RobJansen62/Analog-Digital-Clock/pictures/P1000631.JPG

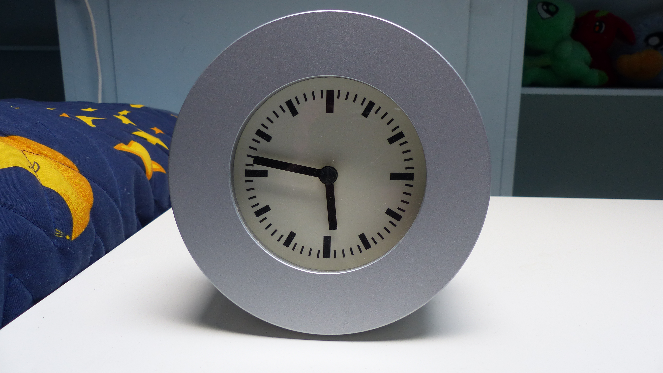
pictures/P1000631.JPG
