RobJansen62/Analog-Digital-Clock/pictures/P1000633.JPG

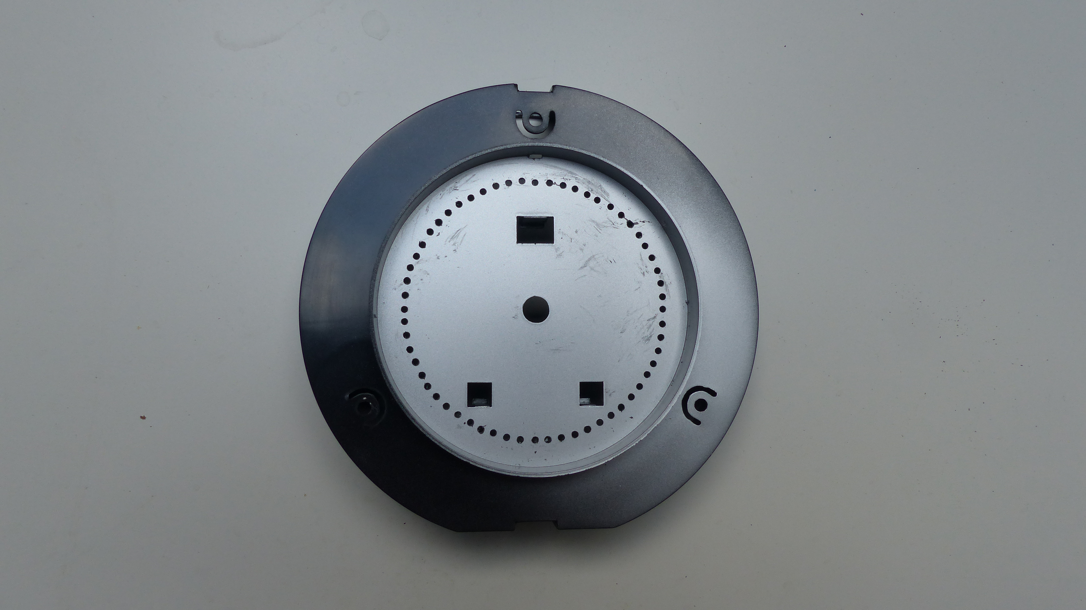
pictures/P1000633.JPG
