RobJansen62/Analog-Digital-Clock/pictures/P1000641.JPG

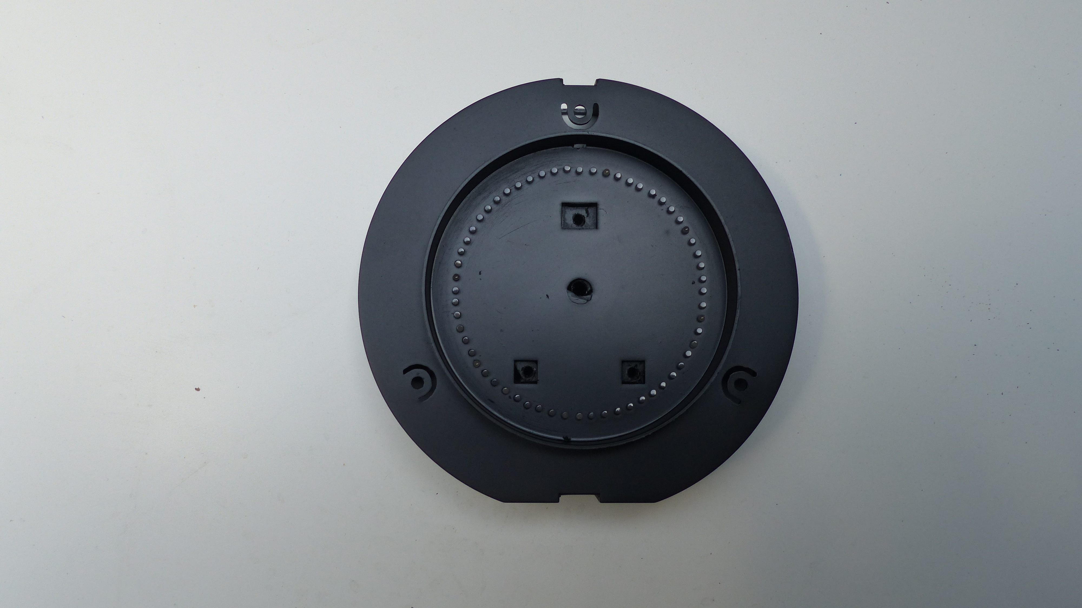
pictures/P1000641.JPG
