RobJansen62/Analog-Digital-Clock/pictures/P1000644.JPG

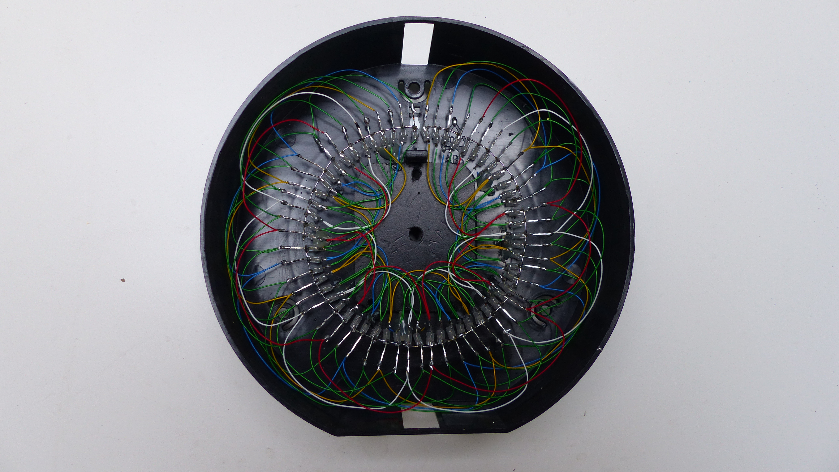
pictures/P1000644.JPG
