RobJansen62/Analog-Digital-Clock/pictures/P1000670.JPG

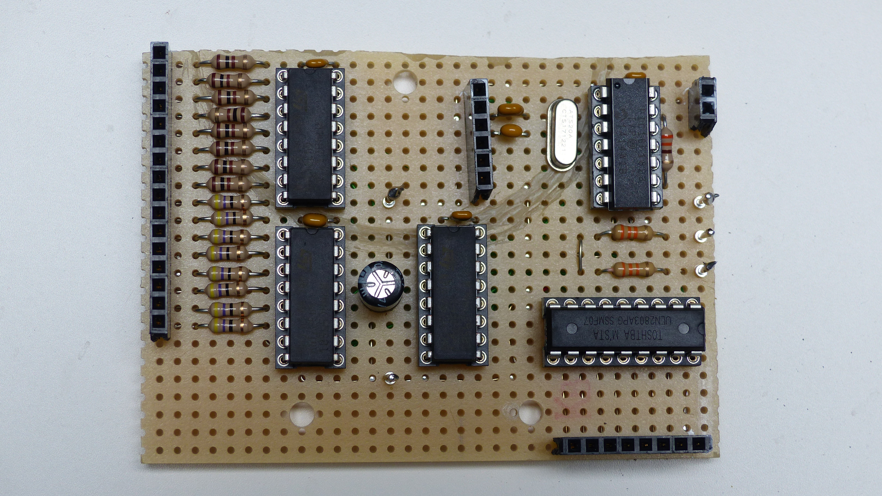
pictures/P1000670.JPG
