RobJansen62/Analog-Digital-Clock/pictures/P1000675.JPG

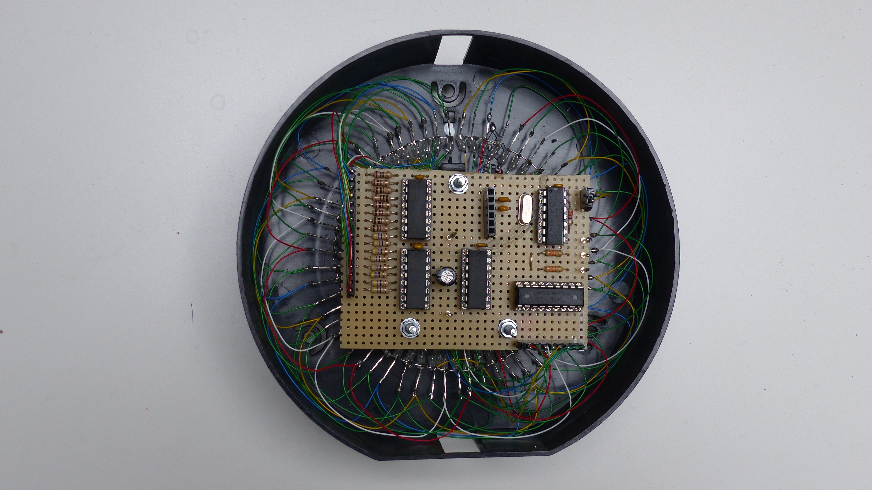
pictures/P1000675.JPG
