RobJansen62/Analog-Digital-Clock/hardware/Analog_Digital_Clock.kicad_sch

## KiCad design hardware/Analog_Digital_Clock.kicad_sch (2025-06-09)

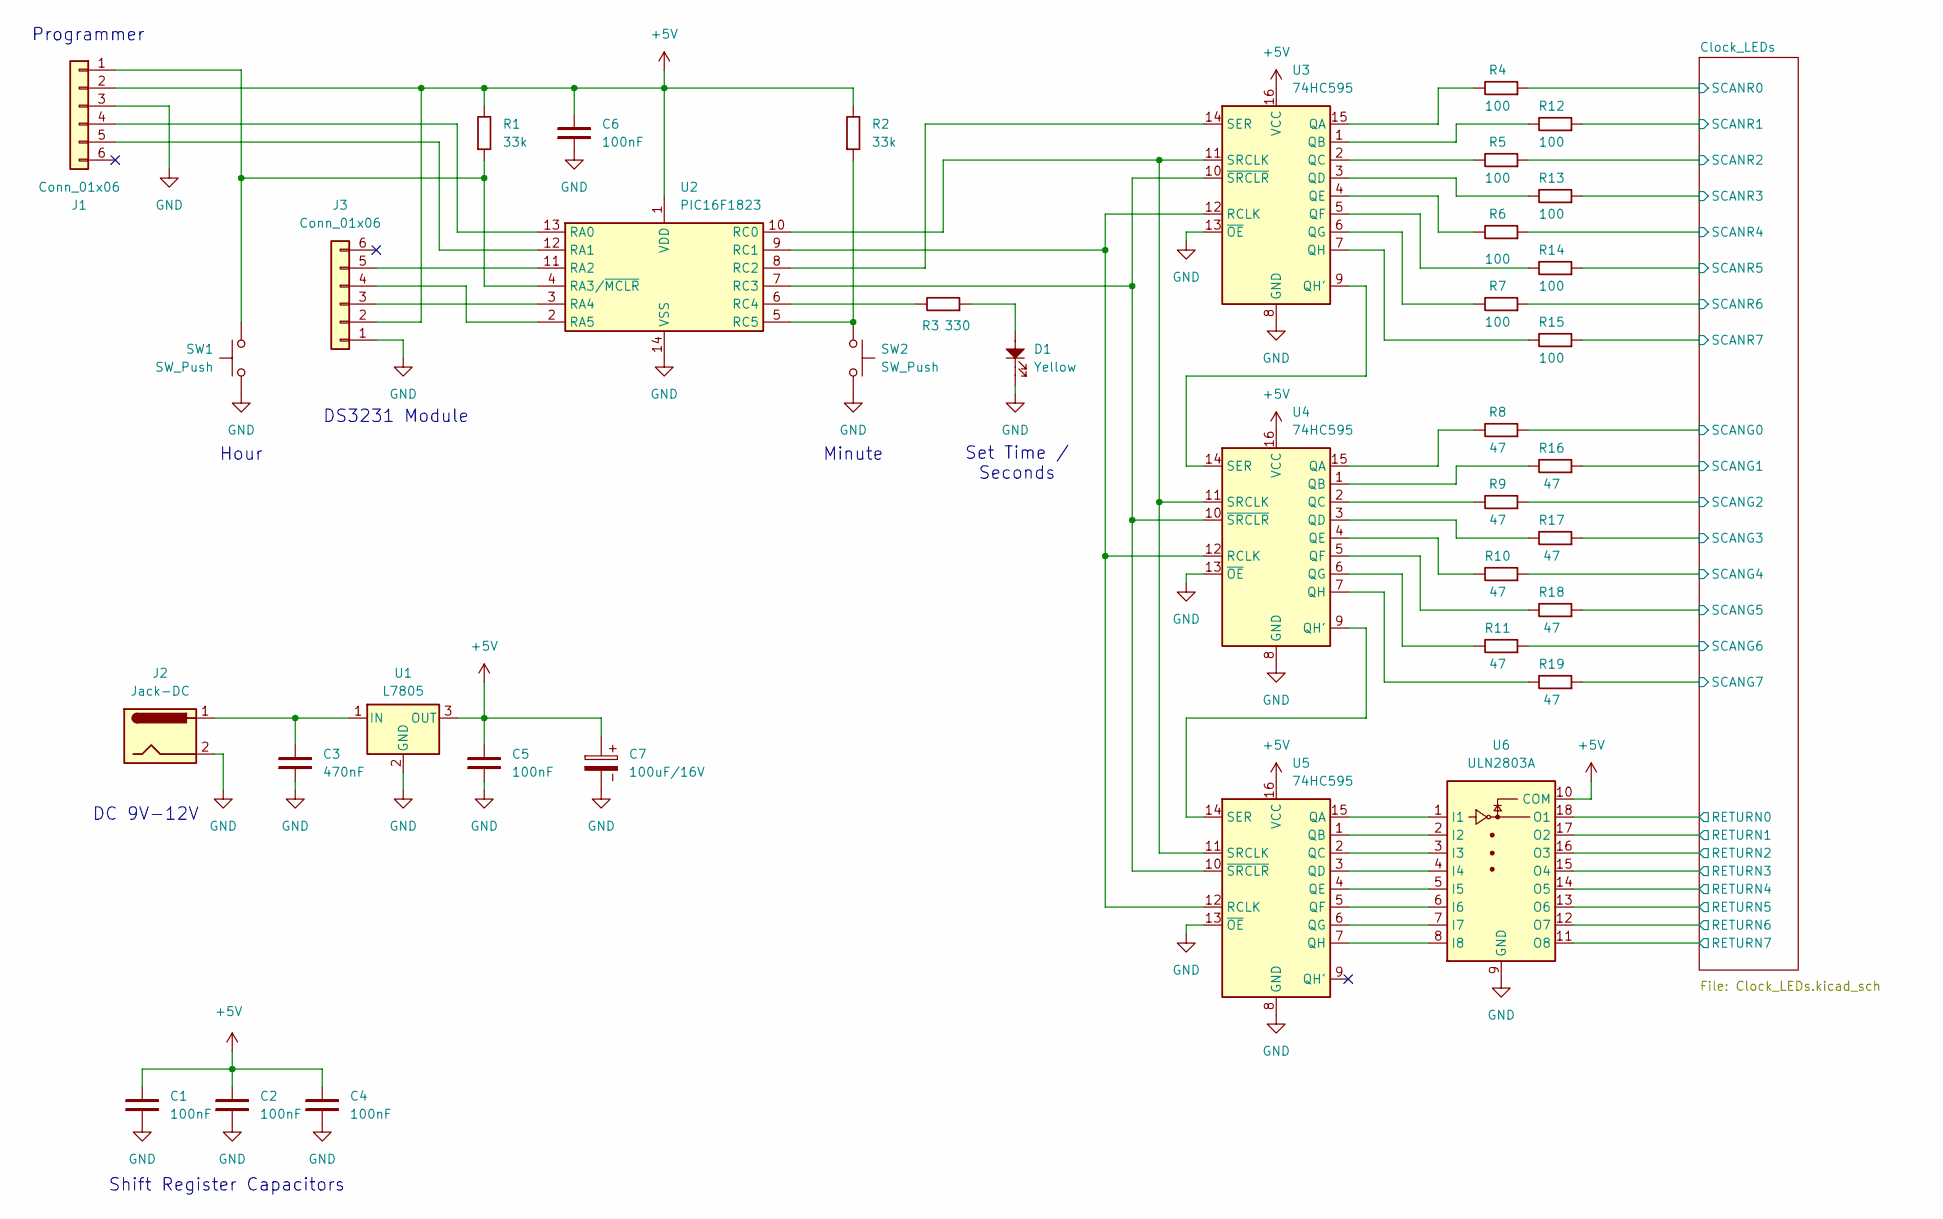
[picture p14: schematic Analog_Digital_Clock.kicad_sch]

Parts:
C1, C2, C4, C5, C6: 100nF; C_Disc_D5.0mm_W2.5mm_P2.50mm
C3: 470nF; C_Disc_D5.0mm_W2.5mm_P2.50mm
C7: 100uF/16V; CP_Radial_D5.0mm_P2.50mm
D1: Yellow; LED_D5.0mm
J1, J3: Conn_01x06
J2: Jack-DC
R1, R2: 33k; R_Axial_DIN0207_L6.3mm_D2.5mm_P10.16mm_Horizontal
R3: 330; R_Axial_DIN0207_L6.3mm_D2.5mm_P10.16mm_Horizontal
R4, R5, R6, R7, R12, R13, R14, R15: 100; R_Axial_DIN0207_L6.3mm_D2.5mm_P10.16mm_Horizontal
R8, R9, R10, R11, R16, R17, R18, R19: 47; R_Axial_DIN0207_L6.3mm_D2.5mm_P10.16mm_Horizontal
SW1, SW2: SW_Push
U1: L7805
U2: PIC16F1823; SOIC-14_3.9x8.7mm_P1.27mm
U3, U4, U5: 74HC595
U6: ULN2803A

Connections:
+5V: C1.2, C2.2, C4.2, C5.2, C6.2, C7.1, J1.2, J3.2, R1.2, R2.2, U1.3 (OUT), U2.1 (VDD), U3.16 (VCC), U4.16 (VCC), U5.16 (VCC), U6.10 (COM)
GND: C1.1, C2.1, C3.1, C4.1, C5.1, C6.1, C7.2, D1.1, J1.3, J2.2, J3.1, SW1.1, SW2.1, U1.2 (GND), U2.14 (VSS), U3.8 (GND), U3.13 (~OE), U4.8 (GND), U4.13 (~OE), U5.8 (GND), U5.13 (~OE), U6.9 (GND)
unnamed: C3.2, J2.1, U1.1 (IN)
unnamed: D1.2, R3.1
unnamed: J1.1, R1.1, SW1.2, U2.4 (RA3/~MCLR)
unnamed: J1.4, U2.13 (RA0)
unnamed: J1.5, U2.12 (RA1)
unnamed: J3.3, U2.3 (RA4)
unnamed: J3.4, U2.2 (RA5)
unnamed: J3.5, U2.11 (RA2)
unnamed: R2.1, SW2.2, U2.5 (RC5)
unnamed: R3.2, U2.6 (RC4)
unnamed: R4.2, U3.15 (QA)
unnamed: R5.2, U3.2 (QC)
unnamed: R6.2, U3.4 (QE)
unnamed: R7.2, U3.6 (QG)
unnamed: R8.2, U4.15 (QA)
unnamed: R9.2, U4.2 (QC)
unnamed: R10.2, U4.4 (QE)
unnamed: R11.2, U4.6 (QG)
unnamed: R12.2, U3.1 (QB)
unnamed: R13.2, U3.3 (QD)
unnamed: R14.2, U3.5 (QF)
unnamed: R15.2, U3.7 (QH)
unnamed: R16.2, U4.1 (QB)
unnamed: R17.2, U4.3 (QD)
unnamed: R18.2, U4.5 (QF)
unnamed: R19.2, U4.7 (QH)
unnamed: U2.7 (RC3), U3.10 (~SRCLR), U4.10 (~SRCLR), U5.10 (~SRCLR)
unnamed: U2.8 (RC2), U3.14 (SER)
unnamed: U2.9 (RC1), U3.12 (RCLK), U4.12 (RCLK), U5.12 (RCLK)
unnamed: U2.10 (RC0), U3.11 (SRCLK), U4.11 (SRCLK), U5.11 (SRCLK)
unnamed: U3.9 (QH'), U4.14 (SER)
unnamed: U4.9 (QH'), U5.14 (SER)
unnamed: U5.1 (QB), U6.2 (I2)
unnamed: U5.2 (QC), U6.3 (I3)
unnamed: U5.3 (QD), U6.4 (I4)
unnamed: U5.4 (QE), U6.5 (I5)
unnamed: U5.5 (QF), U6.6 (I6)
unnamed: U5.6 (QG), U6.7 (I7)
unnamed: U5.7 (QH), U6.8 (I8)
unnamed: U5.15 (QA), U6.1 (I1)
RETURN0: U6.18 (O1)
RETURN1: U6.17 (O2)
RETURN2: U6.16 (O3)
RETURN3: U6.15 (O4)
RETURN4: U6.14 (O5)
RETURN5: U6.13 (O6)
RETURN6: U6.12 (O7)
RETURN7: U6.11 (O8)
SCANG0: R8.1
SCANG1: R16.1
SCANG2: R9.1
SCANG3: R17.1
SCANG4: R10.1
SCANG5: R18.1
SCANG6: R11.1
SCANG7: R19.1
SCANR0: R4.1
SCANR1: R12.1
SCANR2: R5.1
SCANR3: R13.1
SCANR4: R6.1
SCANR5: R14.1
SCANR6: R7.1
SCANR7: R15.1

Notes on the sheet:
Hour
Set Time / Seconds
Shift Register Capacitors
Minute
DS3231 Module
DC 9V-12V
Programmer
