RobJansen62/Analog-Digital-Clock/hardware/Clock_LEDs.kicad_sch

## KiCad design hardware/Clock_LEDs.kicad_sch (2025-06-09)

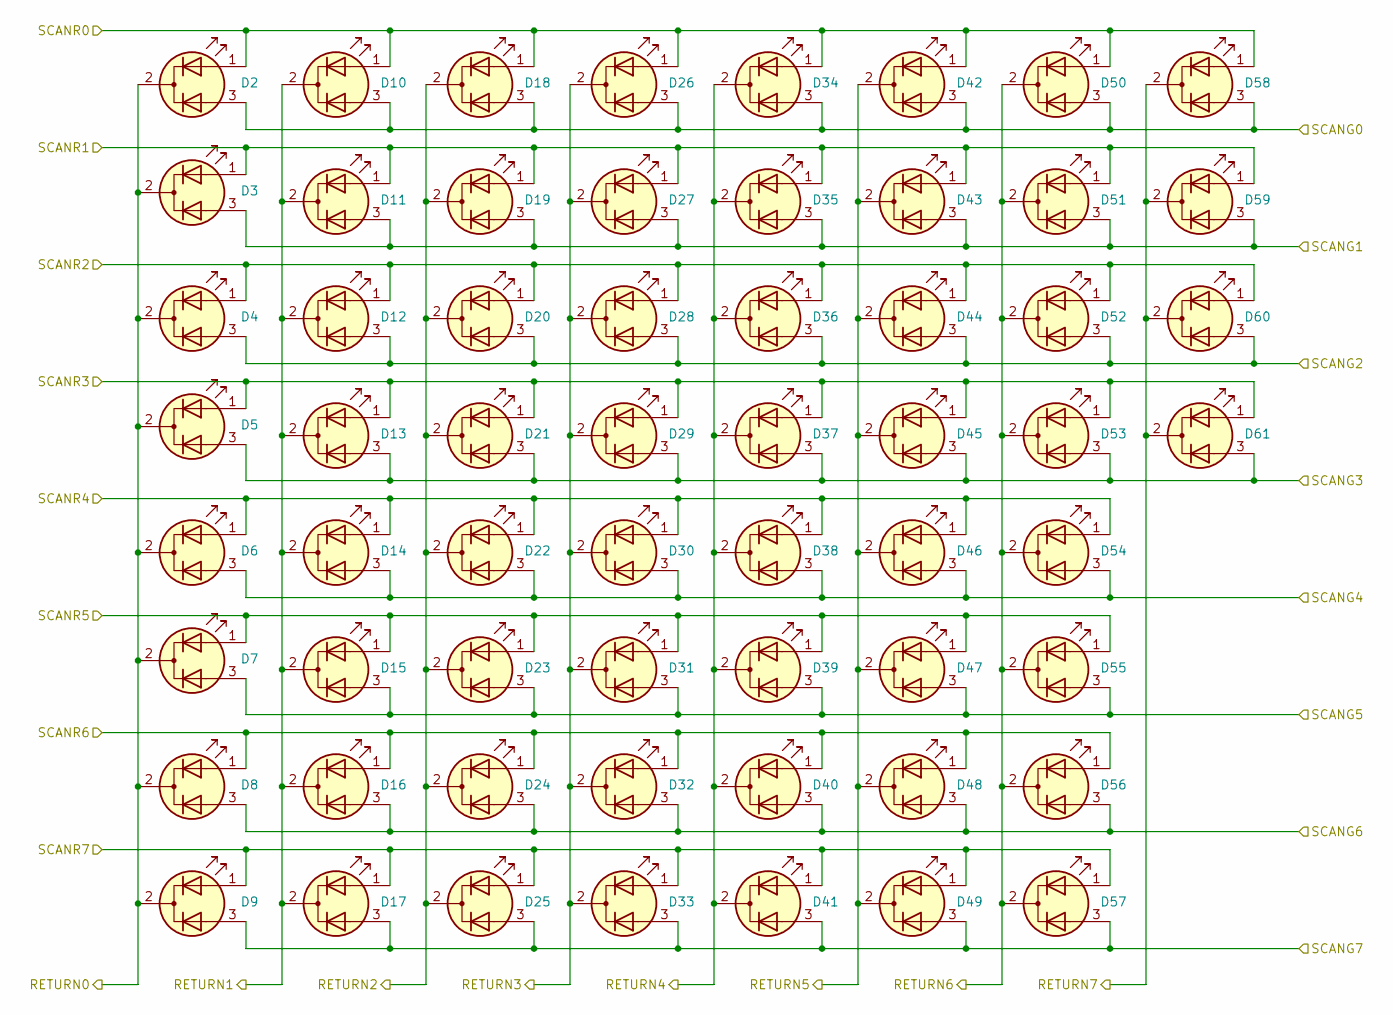
[picture p15: schematic Clock_LEDs.kicad_sch]

Parts:
D2, D3, D4, D5, D6, D7, D8, D9, D10, D11, D12, D13, D14, D15, D16, D17, D18, D19, D20, D21, D22, D23, D24, D25, D26, D27, D28, D29, D30, D31, D32, D33, D34, D35, D36, D37, D38, D39, D40, D41, D42, D43, D44, D45, D46, D47, D48, D49, D50, D51, D52, D53, D54, D55, D56, D57, D58, D59, D60, D61: LED_RG

Connections:
RETURN0: D2.2 (K), D3.2 (K), D4.2 (K), D5.2 (K), D6.2 (K), D7.2 (K), D8.2 (K), D9.2 (K)
RETURN1: D10.2 (K), D11.2 (K), D12.2 (K), D13.2 (K), D14.2 (K), D15.2 (K), D16.2 (K), D17.2 (K)
RETURN2: D18.2 (K), D19.2 (K), D20.2 (K), D21.2 (K), D22.2 (K), D23.2 (K), D24.2 (K), D25.2 (K)
RETURN3: D26.2 (K), D27.2 (K), D28.2 (K), D29.2 (K), D30.2 (K), D31.2 (K), D32.2 (K), D33.2 (K)
RETURN4: D34.2 (K), D35.2 (K), D36.2 (K), D37.2 (K), D38.2 (K), D39.2 (K), D40.2 (K), D41.2 (K)
RETURN5: D42.2 (K), D43.2 (K), D44.2 (K), D45.2 (K), D46.2 (K), D47.2 (K), D48.2 (K), D49.2 (K)
RETURN6: D50.2 (K), D51.2 (K), D52.2 (K), D53.2 (K), D54.2 (K), D55.2 (K), D56.2 (K), D57.2 (K)
RETURN7: D58.2 (K), D59.2 (K), D60.2 (K), D61.2 (K)
SCANG0: D2.3 (A2), D10.3 (A2), D18.3 (A2), D26.3 (A2), D34.3 (A2), D42.3 (A2), D50.3 (A2), D58.3 (A2)
SCANG1: D3.3 (A2), D11.3 (A2), D19.3 (A2), D27.3 (A2), D35.3 (A2), D43.3 (A2), D51.3 (A2), D59.3 (A2)
SCANG2: D4.3 (A2), D12.3 (A2), D20.3 (A2), D28.3 (A2), D36.3 (A2), D44.3 (A2), D52.3 (A2), D60.3 (A2)
SCANG3: D5.3 (A2), D13.3 (A2), D21.3 (A2), D29.3 (A2), D37.3 (A2), D45.3 (A2), D53.3 (A2), D61.3 (A2)
SCANG4: D6.3 (A2), D14.3 (A2), D22.3 (A2), D30.3 (A2), D38.3 (A2), D46.3 (A2), D54.3 (A2)
SCANG5: D7.3 (A2), D15.3 (A2), D23.3 (A2), D31.3 (A2), D39.3 (A2), D47.3 (A2), D55.3 (A2)
SCANG6: D8.3 (A2), D16.3 (A2), D24.3 (A2), D32.3 (A2), D40.3 (A2), D48.3 (A2), D56.3 (A2)
SCANG7: D9.3 (A2), D17.3 (A2), D25.3 (A2), D33.3 (A2), D41.3 (A2), D49.3 (A2), D57.3 (A2)
SCANR0: D2.1 (A1), D10.1 (A1), D18.1 (A1), D26.1 (A1), D34.1 (A1), D42.1 (A1), D50.1 (A1), D58.1 (A1)
SCANR1: D3.1 (A1), D11.1 (A1), D19.1 (A1), D27.1 (A1), D35.1 (A1), D43.1 (A1), D51.1 (A1), D59.1 (A1)
SCANR2: D4.1 (A1), D12.1 (A1), D20.1 (A1), D28.1 (A1), D36.1 (A1), D44.1 (A1), D52.1 (A1), D60.1 (A1)
SCANR3: D5.1 (A1), D13.1 (A1), D21.1 (A1), D29.1 (A1), D37.1 (A1), D45.1 (A1), D53.1 (A1), D61.1 (A1)
SCANR4: D6.1 (A1), D14.1 (A1), D22.1 (A1), D30.1 (A1), D38.1 (A1), D46.1 (A1), D54.1 (A1)
SCANR5: D7.1 (A1), D15.1 (A1), D23.1 (A1), D31.1 (A1), D39.1 (A1), D47.1 (A1), D55.1 (A1)
SCANR6: D8.1 (A1), D16.1 (A1), D24.1 (A1), D32.1 (A1), D40.1 (A1), D48.1 (A1), D56.1 (A1)
SCANR7: D9.1 (A1), D17.1 (A1), D25.1 (A1), D33.1 (A1), D41.1 (A1), D49.1 (A1), D57.1 (A1)
